neuroidss/FreeEEG32-beta/SetupGuides/images/2.7.PNG

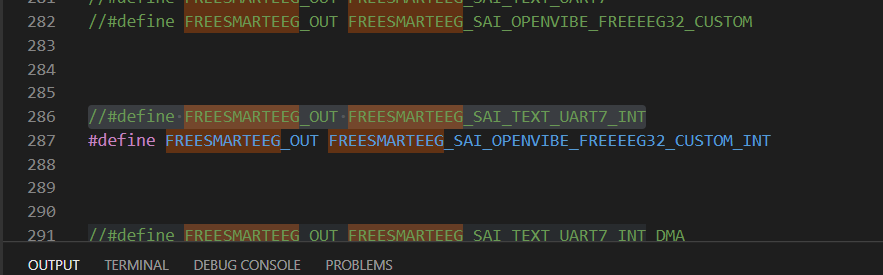
SetupGuides/images/2.7.PNG
