neuroidss/FreeEEG32-beta/SetupGuides/images/test1_2.jpg

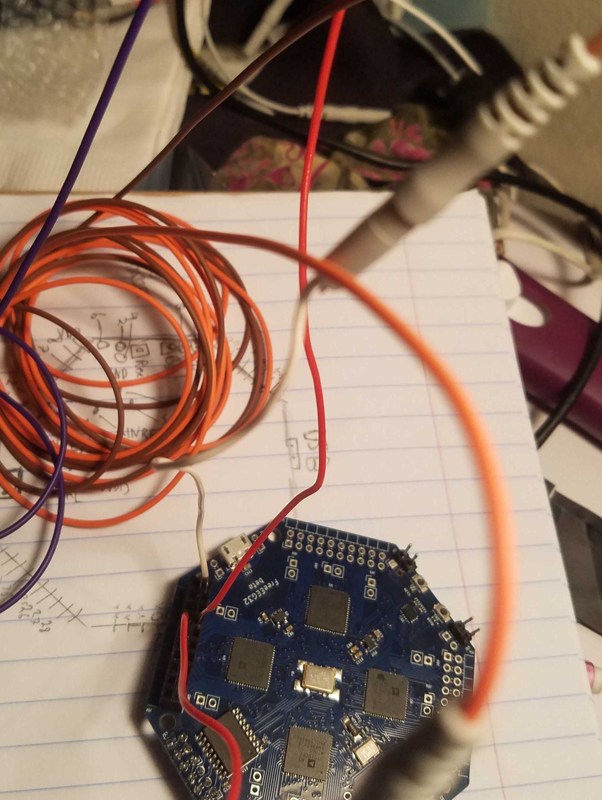
SetupGuides/images/test1_2.jpg
