neuroidss/FreeEEG32-beta/Firmware/AC6/STM32H743ZI_alpha1.5_SD_CDC/Src/ad7779.c

/***************************************************************************//**
 *   @file   ad7779.c
 *   @brief  Implementation of AD7779 Driver.
 *   @author DBogdan (dragos.bogdan@analog.com)
********************************************************************************
 * Copyright 2016(c) Analog Devices, Inc.
 *
 * All rights reserved.
 *
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
 * THIS SOFTWARE IS PROVIDED BY ANALOG DEVICES "AS IS" AND ANY EXPRESS OR
 * IMPLIED WARRANTIES, INCLUDING, BUT NOT LIMITED TO, NON-INFRINGEMENT,
 * MERCHANTABILITY AND FITNESS FOR A PARTICULAR PURPOSE ARE DISCLAIMED.
 * IN NO EVENT SHALL ANALOG DEVICES BE LIABLE FOR ANY DIRECT, INDIRECT,
 * INCIDENTAL, SPECIAL, EXEMPLARY, OR CONSEQUENTIAL DAMAGES (INCLUDING, BUT NOT
 * LIMITED TO, INTELLECTUAL PROPERTY RIGHTS, PROCUREMENT OF SUBSTITUTE GOODS OR
 * SERVICES; LOSS OF USE, DATA, OR PROFITS; OR BUSINESS INTERRUPTION) HOWEVER
 * CAUSED AND ON ANY THEORY OF LIABILITY, WHETHER IN CONTRACT, STRICT LIABILITY,
 * OR TORT (INCLUDING NEGLIGENCE OR OTHERWISE) ARISING IN ANY WAY OUT OF THE USE
 * OF THIS SOFTWARE, EVEN IF ADVISED OF THE POSSIBILITY OF SUCH DAMAGE.
*******************************************************************************/

/******************************************************************************/
/***************************** Include Files **********************************/
/******************************************************************************/
#include <stdint.h>
#include <stdio.h>
#include <stdlib.h>
#include "platform_drivers.h"
#include "ad7779.h"

/******************************************************************************/
/*************************** Constants Definitions ****************************/
/******************************************************************************/
const uint8_t pin_mode_options[16][4] = {
/*	GAIN_1	GAIN_2	GAIN_4	GAIN_8 */
	{0x03,	0xFF,	0x07,	0xFF},	// DEC_RATE_128, HIGH_RES, EXT_REF
	{0x0A,	0xFF,	0xFF,	0xFF},	// DEC_RATE_128, HIGH_RES, INT_REF
	{0x0D,	0xFF,	0xFF,	0xFF},	// DEC_RATE_128, LOW_PWR, EXT_REF
	{0x0E,	0xFF,	0xFF,	0xFF},	// DEC_RATE_128, LOW_PWR, INT_REF
	{0x02,	0x04,	0x06,	0xFF},	// DEC_RATE_256, HIGH_RES, EXT_REF
	{0x09,	0xFF,	0xFF,	0xFF},	// DEC_RATE_256, HIGH_RES, INT_REF
	{0x0C,	0xFF,	0xFF,	0xFF},	// DEC_RATE_256, LOW_PWR, EXT_REF
	{0x0F,	0xFF,	0xFF,	0xFF},	// DEC_RATE_256, LOW_PWR, INT_REF
	{0x01,	0xFF,	0x05,	0xFF},	// DEC_RATE_512, HIGH_RES, EXT_REF
	{0x08,	0xFF,	0xFF,	0xFF},	// DEC_RATE_512, HIGH_RES, INT_REF
	{0x08,	0xFF,	0xFF,	0xFF},	// DEC_RATE_512, LOW_PWR, EXT_REF
	{0xFF,	0xFF,	0xFF,	0xFF},	// DEC_RATE_512, LOW_PWR, INT_REF
	{0x00,	0xFF,	0xFF,	0xFF},	// DEC_RATE_1024, HIGH_RES, EXT_REF
	{0xFF,	0xFF,	0xFF,	0xFF},	// DEC_RATE_1024, HIGH_RES, INT_REF
	{0xFF,	0xFF,	0xFF,	0xFF},	// DEC_RATE_1024, LOW_PWR, EXT_REF
	{0xFF,	0xFF,	0xFF,	0xFF},	// DEC_RATE_1024, LOW_PWR, INT_REF	
};

/******************************************************************************/
/************************** Functions Implementation **************************/
/******************************************************************************/
/**
 * Compute CRC8 checksum.
 * @param data - The data buffer.
 * @param data_size - The size of the data buffer.
 * @return CRC8 checksum.
 */
uint8_t ad7779_compute_crc8(uint8_t *data,
							uint8_t data_size)
{
	uint8_t i;
	uint8_t crc = 0;

	while (data_size) {
		for (i = 0x80; i != 0; i >>= 1) {
			if (((crc & 0x80) != 0) != ((*data & i) != 0)) {
				crc <<= 1;
				crc ^= AD7779_CRC8_POLY;
			} else
				crc <<= 1;
		}
		data++;
		data_size--;
	}

	return crc;
}

/**
 * SPI internal register read from device.
 * @param dev - The device structure.
 * @param reg_addr - The register address.
 * @param reg_data - The register data.
 * @return SUCCESS in case of success, negative error code otherwise.
 */
int32_t ad7779_spi_int_reg_read(ad7779_dev *dev,
								uint8_t reg_addr,
								uint8_t *reg_data)
{
  uint8_t txbuf[3];
  uint8_t rxbuf[3];
	uint8_t buf_size = 2;
	uint8_t crc;
	int32_t ret;

	txbuf[0] = 0x80 | (reg_addr & 0x7F);
	txbuf[1] = 0x00;
	txbuf[2] = 0x00;
	if (dev->spi_crc_en == AD7779_ENABLE)
		buf_size = 3;
	ret = spi_write_and_read(dev->spi_dev.dev, dev->spi_dev.chip_select_port, dev->spi_dev.chip_select_pin, txbuf, rxbuf, buf_size);

	*reg_data = rxbuf[1];
	if (dev->spi_crc_en == AD7779_ENABLE) {
		rxbuf[0] = 0x80 | (reg_addr & 0x7F);
		crc = ad7779_compute_crc8(&rxbuf[0], 2);
		if (crc != rxbuf[2]) {
			printf("%s: CRC Error.\n", __func__);
			ret = FAILURE;
		}
	}

	return ret;
}

/**
 * SPI internal register write to device.
 * @param dev - The device structure.
 * @param reg_addr - The register address.
 * @param reg_data - The register data.
 * @return SUCCESS in case of success, negative error code otherwise.
 */
int32_t ad7779_spi_int_reg_write(ad7779_dev *dev,
								 uint8_t reg_addr,
								 uint8_t reg_data)
{
  uint8_t txbuf[3];
  uint8_t rxbuf[3];
	uint8_t buf_size = 2;
	int32_t ret;

	txbuf[0] = 0x00 | (reg_addr & 0x7F);
	txbuf[1] = reg_data;
	if (dev->spi_crc_en == AD7779_ENABLE) {
		txbuf[2] = ad7779_compute_crc8(&txbuf[0], 2);
		buf_size = 3;
	}
	ret = spi_write_and_read(dev->spi_dev.dev, dev->spi_dev.chip_select_port, dev->spi_dev.chip_select_pin, txbuf, rxbuf, buf_size);
	dev->cached_reg_val[reg_addr] = reg_data;

	return ret;
}

/**
 * SPI internal register read from device using a mask.
 * @param dev - The device structure.
 * @param reg_addr - The register address.
 * @param mask - The mask.
 * @param data - The register data.
 * @return SUCCESS in case of success, negative error code otherwise.
 */
int32_t ad7779_spi_int_reg_read_mask(ad7779_dev *dev,
									 uint8_t reg_addr,
									 uint8_t mask,
									 uint8_t *data)
{
	uint8_t reg_data;
	int32_t ret;

	ret = ad7779_spi_int_reg_read(dev, reg_addr, &reg_data);
	*data = (reg_data & mask);

	return ret;
}

/**
 * SPI internal register write to device using a mask.
 * @param dev - The device structure.
 * @param reg_addr - The register address.
 * @param mask - The mask.
 * @param data - The register data.
 * @return SUCCESS in case of success, negative error code otherwise.
 */
int32_t ad7779_spi_int_reg_write_mask(ad7779_dev *dev,
									  uint8_t reg_addr,
									  uint8_t mask,
									  uint8_t data)
{
	uint8_t reg_data;
	int32_t ret;

	reg_data = dev->cached_reg_val[reg_addr];
	reg_data &= ~mask;
	reg_data |= data;
	ret = ad7779_spi_int_reg_write(dev, reg_addr, reg_data);

	return ret;
}

/**
 * SPI SAR conversion code read.
 * @param dev - The device structure.
 * @param mux_next_conv - The SAR mux input configuration for the next
 *						  conversion.
 * 						  Accepted values: AD7779_AUXAINP_AUXAINN
 *										   AD7779_DVBE_AVSSX
 *										   AD7779_REF1P_REF1N
 *										   AD7779_REF2P_REF2N
 *										   AD7779_REF_OUT_AVSSX
 *										   AD7779_VCM_AVSSX
 *										   AD7779_AREG1CAP_AVSSX_ATT
 *										   AD7779_AREG2CAP_AVSSX_ATT
 *										   AD7779_DREGCAP_DGND_ATT
 *										   AD7779_AVDD1A_AVSSX_ATT
 *										   AD7779_AVDD1B_AVSSX_ATT
 *										   AD7779_AVDD2A_AVSSX_ATT
 *										   AD7779_AVDD2B_AVSSX_ATT
 *										   AD7779_IOVDD_DGND_ATT
 *										   AD7779_AVDD4_AVSSX
 *										   AD7779_DGND_AVSS1A_ATT
 *										   AD7779_DGND_AVSS1B_ATT
 *										   AD7779_DGND_AVSSX_ATT
 *										   AD7779_AVDD4_AVSSX_ATT
 *										   AD7779_REF1P_AVSSX
 *										   AD7779_REF2P_AVSSX
 *										   AD7779_AVSSX_AVDD4_ATT
 * @param sar_code - SAR conversion code.
 * @return SUCCESS in case of success, negative error code otherwise.
 */
int32_t ad7779_spi_sar_read_code(ad7779_dev *dev,
								 ad7779_sar_mux mux_next_conv,
								 uint16_t *sar_code)
{
  uint8_t txbuf[3];
  uint8_t rxbuf[3];
	uint8_t buf_size = 2;
	uint8_t crc;
	int32_t ret;

	txbuf[0] = 0x00 | (AD7779_REG_GLOBAL_MUX_CONFIG & 0x7F);
	txbuf[1] = AD7779_GLOBAL_MUX_CTRL(mux_next_conv);
	if (dev->spi_crc_en == AD7779_ENABLE) {
		txbuf[2] = ad7779_compute_crc8(&txbuf[0], 2);
		buf_size = 3;
	}
	ret = spi_write_and_read(dev->spi_dev.dev, dev->spi_dev.chip_select_port, dev->spi_dev.chip_select_pin, txbuf, rxbuf, buf_size);
	dev->cached_reg_val[AD7779_REG_GLOBAL_MUX_CONFIG] =
									AD7779_GLOBAL_MUX_CTRL(mux_next_conv);
	rxbuf[0] = rxbuf[0] & 0x0F;
	*sar_code = (rxbuf[0] << 8) | rxbuf[1];
	if (dev->spi_crc_en == AD7779_ENABLE) {
		crc = ad7779_compute_crc8(&rxbuf[0], 2);
		if (crc != rxbuf[2]) {
			printf("%s: CRC Error.\n", __func__);
			ret = FAILURE;
		}
	}

	return ret;
}

/**
 * Set SPI operation mode.
 * @param dev - The device structure.
 * @param mode - The SPI operation mode.
 *				 Accepted values: AD7779_INT_REG
 *								  AD7779_SD_CONV
 *								  AD7779_SAR_CONV
 * @return SUCCESS in case of success, negative error code otherwise.
 */
int32_t ad7779_set_spi_op_mode(ad7779_dev *dev,
							   ad7779_spi_op_mode mode)
{
	int32_t ret;
	uint8_t cfg_2;
	uint8_t cfg_3;

	switch (mode) {
	case AD7779_SD_CONV:
		cfg_2 = 0;
		cfg_3 = AD7779_SPI_SLAVE_MODE_EN;
		break;
	case AD7779_SAR_CONV:
		cfg_2 = AD7779_SAR_DIAG_MODE_EN;
		cfg_3 = 0;
		break;
	default:	// AD7779_INT_REG
		cfg_2 = 0;
		cfg_3 = 0;
	}
	ret = ad7779_spi_int_reg_write_mask(dev,
										AD7779_REG_GENERAL_USER_CONFIG_2,
										AD7779_SAR_DIAG_MODE_EN,
										cfg_2);
	ret |= ad7779_spi_int_reg_write_mask(dev,
										 AD7779_REG_GENERAL_USER_CONFIG_3,
										 AD7779_SPI_SLAVE_MODE_EN,
										 cfg_3);
	dev->spi_op_mode = mode;

	return ret;
}

/**
 * Get SPI operation mode.
 * @param dev - The device structure.
 * @param mode - The SPI operation mode.
 * @return SUCCESS in case of success, negative error code otherwise.
 */
int32_t ad7779_get_spi_op_mode(ad7779_dev *dev,
							   ad7779_spi_op_mode *mode)
{
	*mode = dev->spi_op_mode;

	return SUCCESS;
}

/**
 * Update the state of the MODEx pins according to the settings specified in
 * the device structure.
 * @param dev - The device structure.
 * @return SUCCESS in case of success, negative error code otherwise.
 */
int32_t ad7779_do_update_mode_pins(ad7779_dev *dev)
{
	int32_t ret;
	uint8_t option_index;
	uint8_t mode;

	if (!(dev->gain[AD7779_CH0] == dev->gain[AD7779_CH1] ==
		  dev->gain[AD7779_CH2] == dev->gain[AD7779_CH3] == AD7779_GAIN_1))
		goto error;

	if (!(dev->gain[AD7779_CH4] == dev->gain[AD7779_CH5] ==
		  dev->gain[AD7779_CH6] == dev->gain[AD7779_CH6]))
		goto error;

	switch (dev->dec_rate_int) {
	case 128:
		option_index = 0;
		break;
	case 256:
		option_index = 4;
		break;
	case 512:
		option_index = 8;
		break;
	case 1024:
		option_index = 12;
		break;
	default:
		goto error;
	}

	if (dev->pwr_mode == AD7779_HIGH_RES)
		if (dev->ref_type == AD7779_EXT_REF)
			mode = pin_mode_options[option_index + 0][dev->gain[AD7779_CH4]];
		else
			mode = pin_mode_options[option_index + 1][dev->gain[AD7779_CH4]];
	else
		if (dev->ref_type == AD7779_EXT_REF)
			mode = pin_mode_options[option_index + 2][dev->gain[AD7779_CH4]];
		else
			mode = pin_mode_options[option_index + 3][dev->gain[AD7779_CH4]];

	if (mode == 0xFF)
	  goto error;

	ret = gpio_set_value(&dev->gpio_dev,
					dev->gpio_mode0,
					((mode & 0x01) >> 0));
	ret |= gpio_set_value(&dev->gpio_dev,
					dev->gpio_mode1,
					((mode & 0x02) >> 1));
	ret |= gpio_set_value(&dev->gpio_dev,
					dev->gpio_mode2,
					((mode & 0x04) >> 2));
	ret |= gpio_set_value(&dev->gpio_dev,
					dev->gpio_mode3,
					((mode & 0x08) >> 3));

	/* All the pins that define the AD7779 configuration mode are re-evaluated
	 * every time SYNC_IN pin is pulsed. */
	ret |= gpio_set_value(&dev->gpio_dev, dev->gpio_sync_in, GPIO_LOW);
	mdelay(10);
	ret |= gpio_set_value(&dev->gpio_dev, dev->gpio_sync_in, GPIO_HIGH);

	return ret;

error:
	printf("%s: This setting can't be set in PIN control mode.\n",
		   __func__);
	return FAILURE;
}

/**
 * Set the state (enable, disable) of the channel.
 * @param dev - The device structure.
 * @param ch - The channel number.
 * 			   Accepted values: AD7779_CH0
 * 			   					AD7779_CH1
 * 			   					AD7779_CH2
 * 			   					AD7779_CH3
 * 			   					AD7779_CH4
 * 			   					AD7779_CH5
 * 			   					AD7779_CH6
 * 			   					AD7779_CH7
 * @param state - The channel state.
 * 				  Accepted values: AD7779_ENABLE
 * 								   AD7779_DISABLE
 * @return SUCCESS in case of success, negative error code otherwise.
 */
int32_t ad7779_set_state(ad7779_dev *dev,
						 ad7779_ch ch,
						 ad7779_state state)
{
	int32_t ret;

	ret = ad7779_spi_int_reg_write_mask(dev,
										AD7779_REG_CH_DISABLE,
										AD7779_CH_DISABLE(0x1),
										AD7779_CH_DISABLE(state));
	dev->state[ch] = state;

	return ret;
}

/**
 * Get the state (enable, disable) of the selected channel.
 * @param dev - The device structure.
 * @param ch - The channel number.
 * 			   Accepted values: AD7779_CH0
 * 			   					AD7779_CH1
 * 			   					AD7779_CH2
 * 			   					AD7779_CH3
 * 			   					AD7779_CH4
 * 			   					AD7779_CH5
 * 			   					AD7779_CH6
 * 			   					AD7779_CH7
 * @param state - The channel state.
 * @return SUCCESS in case of success, negative error code otherwise.
 */
int32_t ad7779_get_state(ad7779_dev *dev,
						 ad7779_ch ch,
						 ad7779_state *state)
{
	*state = dev->state[ch];

	return SUCCESS;
}

/**
 * Set the gain of the selected channel.
 * @param dev - The device structure.
 * @param ch - The channel number.
 * 			   Accepted values: AD7779_CH0
 * 			   					AD7779_CH1
 * 			   					AD7779_CH2
 * 			   					AD7779_CH3
 * 			   					AD7779_CH4
 * 			   					AD7779_CH5
 * 			   					AD7779_CH6
 * 			   					AD7779_CH7
 * @param gain - The gain value.
 * 				 Accepted values: AD7779_GAIN_1
 * 								  AD7779_GAIN_2
 * 								  AD7779_GAIN_4
 * 								  AD7779_GAIN_8
 * @return SUCCESS in case of success, negative error code otherwise.
 */
int32_t ad7779_set_gain(ad7779_dev *dev,
						ad7779_ch ch,
						ad7779_gain gain)
{
	int32_t ret;

	if (dev->ctrl_mode == AD7779_PIN_CTRL) {
		if (ch <= AD7779_CH3) {
			dev->gain[AD7779_CH0] = gain;
			dev->gain[AD7779_CH1] = gain;
			dev->gain[AD7779_CH2] = gain;
			dev->gain[AD7779_CH3] = gain;
		} else {
			dev->gain[AD7779_CH4] = gain;
			dev->gain[AD7779_CH5] = gain;
			dev->gain[AD7779_CH6] = gain;
			dev->gain[AD7779_CH7] = gain;
		}
		ret = ad7779_do_update_mode_pins(dev);
	} else {
		dev->gain[ch] = gain;
		ret = ad7779_spi_int_reg_write_mask(dev,
											AD7779_REG_CH_CONFIG(ch),
											AD7779_CH_GAIN(0x3),
											AD7779_CH_GAIN(gain));
	}

	return ret;
}

/**
 * Get the gain of the selected channel.
 * @param dev - The device structure.
 * @param ch - The channel number.
 * 			   Accepted values: AD7779_CH0
 * 			   					AD7779_CH1
 * 			   					AD7779_CH2
 * 			   					AD7779_CH3
 * 			   					AD7779_CH4
 * 			   					AD7779_CH5
 * 			   					AD7779_CH6
 * 			   					AD7779_CH7
 * @param gain - The gain value.
 * @return SUCCESS in case of success, negative error code otherwise.
 */
int32_t ad7779_get_gain(ad7779_dev *dev,
						ad7779_ch ch,
						ad7779_gain *gain)
{
	*gain = dev->gain[ch];

	return SUCCESS;
}

/**
 * Set the decimation rate.
 * @param dev - The device structure.
 * @param integer_val - The integer value.
 * @param decimal_val - The decimal value.
 * @return SUCCESS in case of success, negative error code otherwise.
 */
int32_t ad7779_set_dec_rate(ad7779_dev *dev,
							uint16_t int_val,
							uint16_t dec_val)
{
	int32_t ret;
	uint8_t msb;
	uint8_t lsb;

	if (dev->ctrl_mode == AD7779_PIN_CTRL) {
		switch (int_val) {
		case 128:
			break;
		case 256:
			break;
		case 512:
			break;
		case 1024:
			break;
		default:
			printf("%s: This setting can't be set in PIN control mode.\n",
				   __func__);
			return FAILURE;
		}
		dev->dec_rate_int = int_val;
		dev->dec_rate_int = dec_val;
		ret = ad7779_do_update_mode_pins(dev);
	} else {
		msb = (int_val & 0x0F00) >> 8;
		lsb = (int_val & 0x00FF) >> 0;
		ret = ad7779_spi_int_reg_write(dev,
									   AD7779_REG_SRC_N_MSB,
									   msb);
		ret |= ad7779_spi_int_reg_write(dev,
										AD7779_REG_SRC_N_LSB,
										lsb);
		dec_val = (dec_val * 65536) / 1000;
		msb = (dec_val & 0xFF00) >> 8;
		lsb = (dec_val & 0x00FF) >> 0;
		ret |= ad7779_spi_int_reg_write(dev,
										AD7779_REG_SRC_IF_MSB,
										msb);
		ret |= ad7779_spi_int_reg_write(dev,
										AD7779_REG_SRC_IF_LSB,
										lsb);
		dev->dec_rate_int = int_val;
		dev->dec_rate_int = dec_val;
	}

	return ret;
}

/**
 * Get the decimation rate.
 * @param dev - The device structure.
 * @param integer_val - The integer value.
 * @param decimal_val - The decimal value.
 * @return SUCCESS in case of success, negative error code otherwise.
 */
int32_t ad7779_get_dec_rate(ad7779_dev *dev,
							uint16_t *int_val,
							uint16_t *dec_val)
{
	*int_val = dev->dec_rate_int;
	*dec_val = dev->dec_rate_int;

	return SUCCESS;
}

/**
 * Set the power mode.
 * @param dev - The device structure.
 * @param pwr_mode - The power mode.
 * 					 Accepted values: AD7779_HIGH_RES
 *									  AD7779_LOW_PWR
 * @return SUCCESS in case of success, negative error code otherwise.
 */
int32_t ad7779_set_power_mode(ad7779_dev *dev,
							  ad7779_pwr_mode pwr_mode)
{
	int32_t ret;

	ret = ad7779_spi_int_reg_write_mask(dev,
										AD7779_REG_GENERAL_USER_CONFIG_1,
										AD7779_MOD_POWERMODE,
										pwr_mode ? AD7779_MOD_POWERMODE : 0);
	dev->pwr_mode = pwr_mode;

	return ret;
}

/**
 * Get the power mode.
 * @param dev - The device structure.
 * @param pwr_mode - The power mode.
 * @return SUCCESS in case of success, negative error code otherwise.
 */
int32_t ad7779_get_power_mode(ad7779_dev *dev,
							  ad7779_pwr_mode *pwr_mode)
{
	*pwr_mode = dev->pwr_mode;

	return SUCCESS;
}

/**
 * Set the reference type.
 * @param dev - The device structure.
 * @param pwr_mode - The reference type.
 * 					 Accepted values: AD7779_EXT_REF
 *									  AD7779_INT_REF
 * @return SUCCESS in case of success, negative error code otherwise.
 */
int32_t ad7779_set_reference_type(ad7779_dev *dev,
								  ad7779_ref_type ref_type)
{
	int32_t ret;

	ret = ad7779_spi_int_reg_write_mask(dev,
										AD7779_REG_GENERAL_USER_CONFIG_1,
										AD7779_PDB_REFOUT_BUF,
										ref_type ? AD7779_PDB_REFOUT_BUF : 0);
	dev->ref_type = ref_type;

	return ret;
}

/**
 * Get the reference type.
 * @param dev - The device structure.
 * @param pwr_mode - The reference type.
 * @return SUCCESS in case of success, negative error code otherwise.
 */
int32_t ad7779_get_reference_type(ad7779_dev *dev,
								  ad7779_ref_type *ref_type)
{
	*ref_type = dev->ref_type;

	return SUCCESS;
}

/**
 * Set the DCLK divider.
 * @param dev - The device structure.
 * @param div - The DCLK divider.
 *				Accepted values: AD7779_DCLK_DIV_1
 *								 AD7779_DCLK_DIV_2
 *								 AD7779_DCLK_DIV_4
 *								 AD7779_DCLK_DIV_8
 *								 AD7779_DCLK_DIV_16
 *								 AD7779_DCLK_DIV_32
 *								 AD7779_DCLK_DIV_64
 *								 AD7779_DCLK_DIV_128
 * @return SUCCESS in case of success, negative error code otherwise.
 */
int32_t ad7779_set_dclk_div(ad7779_dev *dev,
							ad7768_dclk_div div)
{
	int32_t ret;

	if (dev->ctrl_mode == AD7779_PIN_CTRL) {
		ret = gpio_set_value(&dev->gpio_dev,
						dev->gpio_dclk0,
						((div & 0x01) >> 0));
		ret |= gpio_set_value(&dev->gpio_dev,
						dev->gpio_dclk1,
						((div & 0x02) >> 1));
		ret |= gpio_set_value(&dev->gpio_dev,
						dev->gpio_dclk2,
						((div & 0x04) >> 2));
	} else {
		ret = ad7779_spi_int_reg_write_mask(dev,
											AD7779_REG_CH_DISABLE,
											AD7779_DCLK_CLK_DIV(0x3),
											AD7779_DCLK_CLK_DIV(div));
	}
	dev->dclk_div = div;

	return ret;
}

/**
 * Get the DCLK divider.
 * @param dev - The device structure.
 * @param div - The DCLK divider.
 * @return SUCCESS in case of success, negative error code otherwise.
 */
int32_t ad7779_get_dclk_div(ad7779_dev *dev,
							ad7768_dclk_div *div)
{
	*div = dev->dclk_div;

	return SUCCESS;
}

/**
 * Set the synchronization offset of the selected channel.
 * @param dev - The device structure.
 * @param ch - The channel number.
 * 			   Accepted values: AD7779_CH0
 * 			   					AD7779_CH1
 * 			   					AD7779_CH2
 * 			   					AD7779_CH3
 * 			   					AD7779_CH4
 * 			   					AD7779_CH5
 * 			   					AD7779_CH6
 * 			   					AD7779_CH7
 * @param sync_offset - The synchronization offset value.
 * @return SUCCESS in case of success, negative error code otherwise.
 */
int32_t ad7779_set_sync_offset(ad7779_dev *dev,
							   ad7779_ch ch,
							   uint8_t sync_offset)
{
	int32_t ret;

	if (dev->ctrl_mode == AD7779_PIN_CTRL) {
		printf("%s: This feature is not available in PIN control mode.\n",
			   __func__);
		return FAILURE;
	}

	ret = ad7779_spi_int_reg_write(dev,
								   AD7779_REG_CH_SYNC_OFFSET(ch),
								   sync_offset);
	dev->sync_offset[ch] = sync_offset;

	return ret;
}

/**
 * Get the synchronization offset of the selected channel.
 * @param dev - The device structure.
 * @param ch - The channel number.
 * 			   Accepted values: AD7779_CH0
 * 			   					AD7779_CH1
 * 			   					AD7779_CH2
 * 			   					AD7779_CH3
 * 			   					AD7779_CH4
 * 			   					AD7779_CH5
 * 			   					AD7779_CH6
 * 			   					AD7779_CH7
 * @param sync_offset - The synchronization offset value.
 * @return SUCCESS in case of success, negative error code otherwise.
 */
int32_t ad7779_get_sync_offset(ad7779_dev *dev,
							   ad7779_ch ch,
							   uint8_t *sync_offset)
{
	if (dev->ctrl_mode == AD7779_PIN_CTRL) {
		printf("%s: This feature is not available in PIN control mode.\n",
			   __func__);
		return FAILURE;
	}

	*sync_offset = dev->sync_offset[ch];

	return SUCCESS;
}

/**
 * Set the offset correction of the selected channel.
 * @param dev - The device structure.
 * @param ch - The channel number.
 * 			   Accepted values: AD7779_CH0
 * 			   					AD7779_CH1
 * 			   					AD7779_CH2
 * 			   					AD7779_CH3
 * 			   					AD7779_CH4
 * 			   					AD7779_CH5
 * 			   					AD7779_CH6
 * 			   					AD7779_CH7
 * @param offset - The offset value.
 * @return SUCCESS in case of success, negative error code otherwise.
 */
int32_t ad7779_set_offset_corr(ad7779_dev *dev,
							   ad7779_ch ch,
							   uint32_t offset)
{
	int32_t ret;
	uint8_t upper_uint8_t;
	uint8_t mid_uint8_t;
	uint8_t lower_uint8_t;

	if (dev->ctrl_mode == AD7779_PIN_CTRL) {
		printf("%s: This feature is not available in PIN control mode.\n",
			   __func__);
		return FAILURE;
	}

	upper_uint8_t = (offset & 0xFF0000) >> 16;
	mid_uint8_t = (offset & 0x00FF00) >> 8;
	lower_uint8_t = (offset & 0x0000FF) >> 0;
	ret = ad7779_spi_int_reg_write(dev,
								   AD7779_REG_CH_OFFSET_UPPER_BYTE(ch),
								   upper_uint8_t);
	ret |= ad7779_spi_int_reg_write(dev,
									AD7779_REG_CH_OFFSET_MID_BYTE(ch),
									mid_uint8_t);
	ret |= ad7779_spi_int_reg_write(dev,
									AD7779_REG_CH_OFFSET_LOWER_BYTE(ch),
									lower_uint8_t);
	dev->offset_corr[ch] = offset;

	return ret;
}

/**
 * Get the offset correction of the selected channel.
 * @param dev - The device structure.
 * @param ch - The channel number.
 * 			   Accepted values: AD7779_CH0
 * 			   					AD7779_CH1
 * 			   					AD7779_CH2
 * 			   					AD7779_CH3
 * 			   					AD7779_CH4
 * 			   					AD7779_CH5
 * 			   					AD7779_CH6
 * 			   					AD7779_CH7
 * @param offset - The offset value.
 * @return SUCCESS in case of success, negative error code otherwise.
 */
int32_t ad7779_get_offset_corr(ad7779_dev *dev,
							   ad7779_ch ch,
							   uint32_t *offset)
{
	if (dev->ctrl_mode == AD7779_PIN_CTRL) {
		printf("%s: This feature is not available in PIN control mode.\n",
			   __func__);
		return FAILURE;
	}

	*offset = dev->offset_corr[ch];

	return SUCCESS;
}

/**
 * Set the gain correction of the selected channel.
 * @param dev - The device structure.
 * @param ch - The channel number.
 * 			   Accepted values: AD7779_CH0
 * 			   					AD7779_CH1
 * 			   					AD7779_CH2
 * 			   					AD7779_CH3
 * 			   					AD7779_CH4
 * 			   					AD7779_CH5
 * 			   					AD7779_CH6
 * 			   					AD7779_CH7
 * @param gain - The gain value.
 * @return SUCCESS in case of success, negative error code otherwise.
 */
int32_t ad7779_set_gain_corr(ad7779_dev *dev,
							 ad7779_ch ch,
							 uint32_t gain)
{
	int32_t ret;
	uint8_t upper_uint8_t;
	uint8_t mid_uint8_t;
	uint8_t lower_uint8_t;

	if (dev->ctrl_mode == AD7779_PIN_CTRL) {
		printf("%s: This feature is not available in PIN control mode.\n",
			   __func__);
		return FAILURE;
	}

	gain &= 0xFFFFFF;
	upper_uint8_t = (gain & 0xff0000) >> 16;
	mid_uint8_t = (gain & 0x00ff00) >> 8;
	lower_uint8_t = (gain & 0x0000ff) >> 0;
	ret = ad7779_spi_int_reg_write(dev,
								   AD7779_REG_CH_GAIN_UPPER_BYTE(ch),
								   upper_uint8_t);
	ret |= ad7779_spi_int_reg_write(dev,
									AD7779_REG_CH_GAIN_MID_BYTE(ch),
									mid_uint8_t);
	ret |= ad7779_spi_int_reg_write(dev,
									AD7779_REG_CH_GAIN_LOWER_BYTE(ch),
									lower_uint8_t);
	dev->gain_corr[ch] = gain;

	return ret;
}

/**
 * Get the gain correction of the selected channel.
 * @param dev - The device structure.
 * @param ch - The channel number.
 * 			   Accepted values: AD7779_CH0
 * 			   					AD7779_CH1
 * 			   					AD7779_CH2
 * 			   					AD7779_CH3
 * 			   					AD7779_CH4
 * 			   					AD7779_CH5
 * 			   					AD7779_CH6
 * 			   					AD7779_CH7
 * @param gain - The gain value.
 * @return SUCCESS in case of success, negative error code otherwise.
 */
int32_t ad7779_get_gain_corr(ad7779_dev *dev,
							 ad7779_ch ch,
							 uint32_t *gain)
{
	if (dev->ctrl_mode == AD7779_PIN_CTRL) {
		printf("%s: This feature is not available in PIN control mode.\n",
			   __func__);
		return FAILURE;
	}

	*gain = dev->gain_corr[ch];

	return SUCCESS;
}

/**
 * Set the reference buffer operation mode of the selected pin.
 * @param dev - The device structure.
 * @param refx_pin - The selected pin.
 * 					 Accepted values: AD7779_REFX_P
 * 									  AD7779_REFX_N
 * @param mode - The reference buffer operation mode.
 * 				 Accepted values: AD7779_REF_BUF_ENABLED
 * 								  AD7779_REF_BUF_PRECHARGED
 * 								  AD7779_REF_BUF_DISABLED
 * @return SUCCESS in case of success, negative error code otherwise.
 */
int32_t ad7779_set_ref_buf_op_mode(ad7779_dev *dev,
								   ad7779_refx_pin refx_pin,
								   ad7779_ref_buf_op_mode mode)
{
	int32_t ret;
	uint8_t config_1;
	uint8_t config_2;

	if (dev->ctrl_mode == AD7779_PIN_CTRL) {
		printf("%s: This feature is not available in PIN control mode.\n",
			   __func__);
		return FAILURE;
	}

	if (refx_pin == AD7779_REFX_P) {
		switch (mode) {
		case AD7779_REF_BUF_ENABLED:
			config_1 = AD7779_REF_BUF_POS_EN;
			config_2 = 0;
			break;
		case AD7779_REF_BUF_PRECHARGED:
			config_1 = AD7779_REF_BUF_POS_EN;
			config_2 = AD7779_REFBUFP_PREQ;
			break;
		default:
			config_1 = 0;
			config_2 = 0;
		}
		ret = ad7779_spi_int_reg_write_mask(dev,
											AD7779_REG_BUFFER_CONFIG_1,
											AD7779_REF_BUF_POS_EN,
											config_1);
		ret |= ad7779_spi_int_reg_write_mask(dev,
											 AD7779_REG_BUFFER_CONFIG_2,
											 AD7779_REFBUFP_PREQ,
											 config_2);
	} else {
		switch (mode) {
		case AD7779_REF_BUF_ENABLED:
			config_1 = AD7779_REF_BUF_NEG_EN;
			config_2 = 0;
			break;
		case AD7779_REF_BUF_PRECHARGED:
			config_1 = AD7779_REF_BUF_NEG_EN;
			config_2 = AD7779_REFBUFN_PREQ;
			break;
		default:
			config_1 = 0;
			config_2 = 0;
		}
		ret = ad7779_spi_int_reg_write_mask(dev,
											AD7779_REG_BUFFER_CONFIG_1,
											AD7779_REF_BUF_NEG_EN,
											config_1);
		ret |= ad7779_spi_int_reg_write_mask(dev,
											 AD7779_REG_BUFFER_CONFIG_2,
											 AD7779_REFBUFN_PREQ,
											 config_2);
	}
	dev->ref_buf_op_mode[refx_pin] = mode;

	return ret;
}

/**
 * Get the reference buffer operation mode of the selected pin.
 * @param dev - The device structure.
 * @param refx_pin - The selected pin.
 * 					 Accepted values: AD7779_REFX_P
 * 									  AD7779_REFX_N
 * @param mode - The reference buffer operation mode.
 * 				 Accepted values: AD7779_REF_BUF_ENABLED
 * 								  AD7779_REF_BUF_PRECHARGED
 * 								  AD7779_REF_BUF_DISABLED
 * @return SUCCESS in case of success, negative error code otherwise.
 */
int32_t ad7779_get_ref_buf_op_mode(ad7779_dev *dev,
								   ad7779_refx_pin refx_pin,
								   ad7779_ref_buf_op_mode *mode)
{
	if (dev->ctrl_mode == AD7779_PIN_CTRL) {
		printf("%s: This feature is not available in PIN control mode.\n",
			   __func__);
		return FAILURE;
	}

	*mode = dev->ref_buf_op_mode[refx_pin];

	return SUCCESS;
}

/**
 * Set the SAR ADC configuration.
 * @param dev - The device structure.
 * @param state - The SAR ADC state.
 * 				  Accepted values: AD7779_ENABLE
 * 								   AD7779_DISABLE
 * @param mux - The SAR mux input configuration.
 * 				Accepted values: AD7779_AUXAINP_AUXAINN
 *								 AD7779_DVBE_AVSSX
 *								 AD7779_REF1P_REF1N
 *								 AD7779_REF2P_REF2N
 *								 AD7779_REF_OUT_AVSSX
 *								 AD7779_VCM_AVSSX
 *								 AD7779_AREG1CAP_AVSSX_ATT
 *								 AD7779_AREG2CAP_AVSSX_ATT
 *								 AD7779_DREGCAP_DGND_ATT
 *								 AD7779_AVDD1A_AVSSX_ATT
 *								 AD7779_AVDD1B_AVSSX_ATT
 *								 AD7779_AVDD2A_AVSSX_ATT
 *								 AD7779_AVDD2B_AVSSX_ATT
 *								 AD7779_IOVDD_DGND_ATT
 *								 AD7779_AVDD4_AVSSX
 *								 AD7779_DGND_AVSS1A_ATT
 *								 AD7779_DGND_AVSS1B_ATT
 *								 AD7779_DGND_AVSSX_ATT
 *								 AD7779_AVDD4_AVSSX_ATT
 *								 AD7779_REF1P_AVSSX
 *								 AD7779_REF2P_AVSSX
 *								 AD7779_AVSSX_AVDD4_ATT
 * @return SUCCESS in case of success, negative error code otherwise.
 */
int32_t ad7779_set_sar_cfg(ad7779_dev *dev,
						   ad7779_state state,
						   ad7779_sar_mux mux)
{
	int32_t ret;

	ret = ad7779_spi_int_reg_write_mask(dev,
										AD7779_REG_GENERAL_USER_CONFIG_1,
										AD7779_PDB_SAR,
										(state == AD7779_ENABLE) ?
												AD7779_PDB_SAR : 0);
	ret |= ad7779_spi_int_reg_write(dev,
									AD7779_REG_GLOBAL_MUX_CONFIG,
									AD7779_GLOBAL_MUX_CTRL(mux));
	dev->sar_state = state;
	dev->sar_mux = mux;

	return ret;
}

/**
 * Get the SAR ADC configuration.
 * @param dev - The device structure.
 * @param state - The SAR ADC state.
 * @param mux - The SAR mux input configuration.
 * @return SUCCESS in case of success, negative error code otherwise.
 */
int32_t ad7779_get_sar_cfg(ad7779_dev *dev,
						   ad7779_state *state,
						   ad7779_sar_mux *mux)
{
	*state = dev->sar_state;
	*mux = dev->sar_mux;

	return SUCCESS;
}

/**
 * Do a single SAR conversion.
 * @param dev - The device structure.
 * @param mux - The SAR mux input configuration.
 * 				Accepted values: AD7779_AUXAINP_AUXAINN
 *								 AD7779_DVBE_AVSSX
 *								 AD7779_REF1P_REF1N
 *								 AD7779_REF2P_REF2N
 *								 AD7779_REF_OUT_AVSSX
 *								 AD7779_VCM_AVSSX
 *								 AD7779_AREG1CAP_AVSSX_ATT
 *								 AD7779_AREG2CAP_AVSSX_ATT
 *								 AD7779_DREGCAP_DGND_ATT
 *								 AD7779_AVDD1A_AVSSX_ATT
 *								 AD7779_AVDD1B_AVSSX_ATT
 *								 AD7779_AVDD2A_AVSSX_ATT
 *								 AD7779_AVDD2B_AVSSX_ATT
 *								 AD7779_IOVDD_DGND_ATT
 *								 AD7779_AVDD4_AVSSX
 *								 AD7779_DGND_AVSS1A_ATT
 *								 AD7779_DGND_AVSS1B_ATT
 *								 AD7779_DGND_AVSSX_ATT
 *								 AD7779_AVDD4_AVSSX_ATT
 *								 AD7779_REF1P_AVSSX
 *								 AD7779_REF2P_AVSSX
 *								 AD7779_AVSSX_AVDD4_ATT
 * @param sar_code - SAR conversion code.
 * @return SUCCESS in case of success, negative error code otherwise.
 */
int32_t ad7779_do_single_sar_conv(ad7779_dev *dev,
								  ad7779_sar_mux mux,
								  uint16_t *sar_code)
{
	ad7779_spi_op_mode restore_spi_op_mode;
	ad7779_state restore_sar_state;
	int32_t ret;

	restore_spi_op_mode = dev->spi_op_mode;
	restore_sar_state = dev->sar_state;
	ret = ad7779_set_sar_cfg(dev, AD7779_ENABLE, mux);
	ret |= ad7779_set_spi_op_mode(dev, AD7779_SAR_CONV);
	ret |= gpio_set_value(&dev->gpio_dev, dev->gpio_convst_sar, GPIO_LOW);
	mdelay(10);	// Acquisition Time = min 500 ns
	ret |= gpio_set_value(&dev->gpio_dev, dev->gpio_convst_sar, GPIO_HIGH);
	mdelay(10);	// Conversion Time = max 3.4 us
	ad7779_spi_sar_read_code(dev, mux, sar_code);
	ret |= ad7779_set_sar_cfg(dev, restore_sar_state, mux);
	ret |= ad7779_set_spi_op_mode(dev, restore_spi_op_mode);

	return ret;
}

/**
 * Do a SPI software reset.
 * @param dev - The device structure.
 * @return SUCCESS in case of success, negative error code otherwise.
 */
int32_t ad7779_do_spi_soft_reset(ad7779_dev *dev)
{
  uint8_t txbuf[8] = {0xFF, 0xFF, 0xFF, 0xFF, 0xFF, 0xFF, 0xFF, 0xFF};
  uint8_t rxbuf[8] = {0xFF, 0xFF, 0xFF, 0xFF, 0xFF, 0xFF, 0xFF, 0xFF};
	int32_t ret;

	/* Keeping the SDI pin high during 64 consecutives clocks generates a
	   software reset */
	ret = spi_write_and_read(dev->spi_dev.dev, dev->spi_dev.chip_select_port, dev->spi_dev.chip_select_pin, txbuf, rxbuf, 8);

	return ret;
}

/**
 * Set the state (enable, disable) of the SINC5 filter.
 * @param dev - The device structure.
 * @param state - The SINC5 filter state.
 * 				  Accepted values: AD7779_ENABLE
 * 								   AD7779_DISABLE
 * @return SUCCESS in case of success, negative error code otherwise.
 */
int32_t ad7771_set_sinc5_filter_state(ad7779_dev *dev,
									  ad7779_state state)
{
	int32_t ret;

	if (dev->ctrl_mode == AD7779_PIN_CTRL) {
		printf("%s: This feature is not available in PIN control mode.\n",
			   __func__);
		return FAILURE;
	}

	ret = ad7779_spi_int_reg_write_mask(dev,
										AD7779_REG_GENERAL_USER_CONFIG_2,
										AD7771_FILTER_MODE,
										(state == AD7779_ENABLE) ?
												AD7771_FILTER_MODE : 0);
	dev->sinc5_state = state;

	return ret;
}

/**
 * Get the state (enable, disable) of the SINC5 filter.
 * @param dev - The device structure.
 * @param state - The SINC5 filter state.
 * @return SUCCESS in case of success, negative error code otherwise.
 */
int32_t ad7771_get_sinc5_filter_state(ad7779_dev *dev,
									  ad7779_state *state)
{
	if (dev->ctrl_mode == AD7779_PIN_CTRL) {
		printf("%s: This feature is not available in PIN control mode.\n",
			   __func__);
		return FAILURE;
	}

	*state = dev->sinc5_state;

	return SUCCESS;
}

/**
 * Initialize the device.
 * @param device - The device structure.
 * @param init_param - The structure that contains the device initial
 * 					   parameters.
 * @return SUCCESS in case of success, negative error code otherwise.
 */
int32_t ad7779_setup(ad7779_dev **device,
					 ad7779_init_param init_param)
{
	ad7779_dev *dev;
	uint8_t i;
	int32_t ret;

  if (!dev)
  {
    dev = (ad7779_dev *)malloc(sizeof(*dev));
  }
//	dev = (ad7779_dev *)malloc(sizeof(*dev));
	if (!dev) {
		return -1;
	}

	/* SPI */
//	dev->spi_dev.chip_select = init_param.spi_chip_select;
//  dev->spi_dev.chip_select_port = init_param.spi_chip_select_port;
//  dev->spi_dev.chip_select_pin = init_param.spi_chip_select_pin;
//	dev->spi_dev.mode = init_param.spi_mode;
//	dev->spi_dev.device_id = init_param.spi_device_id;
	//  dev->spi_dev.type = init_param.spi_type;
	dev->spi_dev = init_param.spi_dev;
	ret = spi_init(dev->spi_dev.dev);
//	dev->gpio_dev.device_id = init_param.gpio_device_id;
//	dev->gpio_dev.type = init_param.gpio_type;
	ret |= gpio_init(&dev->gpio_dev);

/*
	// GPIO
	dev->gpio_reset = init_param.gpio_reset;
	dev->gpio_mode0 = init_param.gpio_mode0;
	dev->gpio_mode1 = init_param.gpio_mode1;
	dev->gpio_mode2 = init_param.gpio_mode2;
	dev->gpio_mode3 = init_param.gpio_mode3;
	dev->gpio_dclk0 = init_param.gpio_dclk0;
	dev->gpio_dclk1 = init_param.gpio_dclk1;
	dev->gpio_dclk2 = init_param.gpio_dclk2;
	dev->gpio_sync_in = init_param.gpio_sync_in;
	dev->gpio_convst_sar = init_param.gpio_convst_sar;

	ret |= gpio_set_direction(&dev->gpio_dev, dev->gpio_reset, GPIO_OUT);
	ret |= gpio_set_value(&dev->gpio_dev, dev->gpio_reset, GPIO_LOW);
	mdelay(10);	// RESET Hold Time = min 2 � MCLK
	ret |= gpio_set_value(&dev->gpio_dev, dev->gpio_reset, GPIO_HIGH);
	mdelay(10);	// RESET Rising Edge to First DRDY = min 225 us
	ret |= gpio_set_direction(&dev->gpio_dev, dev->gpio_mode0, GPIO_OUT);
	ret |= gpio_set_direction(&dev->gpio_dev, dev->gpio_mode1, GPIO_OUT);
	ret |= gpio_set_direction(&dev->gpio_dev, dev->gpio_mode2, GPIO_OUT);
	ret |= gpio_set_direction(&dev->gpio_dev, dev->gpio_mode3, GPIO_OUT);
	ret |= gpio_set_direction(&dev->gpio_dev, dev->gpio_dclk0, GPIO_OUT);
	ret |= gpio_set_direction(&dev->gpio_dev, dev->gpio_dclk1, GPIO_OUT);
	ret |= gpio_set_direction(&dev->gpio_dev, dev->gpio_dclk2, GPIO_OUT);
	ret |= gpio_set_direction(&dev->gpio_dev, dev->gpio_sync_in, GPIO_OUT);
	ret |= gpio_set_value(&dev->gpio_dev, dev->gpio_sync_in, GPIO_HIGH);
	ret |= gpio_set_direction(&dev->gpio_dev, dev->gpio_convst_sar, GPIO_OUT);
	ret |= gpio_set_value(&dev->gpio_dev, dev->gpio_convst_sar, GPIO_HIGH);
*/
	// Device Settings
	dev->ctrl_mode = init_param.ctrl_mode;
	dev->spi_crc_en = AD7779_DISABLE;
	dev->spi_op_mode = AD7779_INT_REG;
	dev->sar_state = AD7779_DISABLE;
	dev->sar_mux = AD7779_AUXAINP_AUXAINN;

  uint8_t reg_data;
  for(uint8_t reg_addr = 0; reg_addr < AD7779_REG_SRC_UPDATE + 1; reg_addr++)
  {
    ret |= ad7779_spi_int_reg_read(dev,reg_addr,&reg_data);
    dev->cached_reg_val[reg_addr] = reg_data;
  }


	if ((dev->ctrl_mode == AD7779_SPI_CTRL) &&
				(init_param.spi_crc_en == AD7779_ENABLE)) {
		ret |= ad7779_spi_int_reg_read(dev,
							AD7779_REG_GEN_ERR_REG_1_EN,
							&dev->cached_reg_val[AD7779_REG_GEN_ERR_REG_1_EN]);
		ret |= ad7779_spi_int_reg_write_mask(dev,
							AD7779_REG_GEN_ERR_REG_1_EN,
							AD7779_SPI_CRC_TEST_EN,
							AD7779_SPI_CRC_TEST_EN);
		dev->spi_crc_en = AD7779_ENABLE;
	}


	if (dev->ctrl_mode == AD7779_SPI_CTRL)
		for (i = AD7779_REG_CH_CONFIG(0); i <= AD7779_REG_SRC_UPDATE; i++)
			ret |= ad7779_spi_int_reg_read(dev, i, &dev->cached_reg_val[i]);

  if(0)
	for (i = AD7779_CH0; i <= AD7779_CH7; i++) {
		dev->state[i] = init_param.state[i];
		if (dev->ctrl_mode == AD7779_SPI_CTRL)
			ret |= ad7779_set_state(dev, (ad7779_ch)i, dev->state[i]);
	}
 
	for (i = AD7779_CH0; i <= AD7779_CH7; i++) {
		dev->gain[i] = init_param.gain[i];
		if (dev->ctrl_mode == AD7779_SPI_CTRL)
			ret |= ad7779_set_gain(dev, (ad7779_ch)i, dev->gain[i]);
	}

	dev->dec_rate_int = init_param.dec_rate_int;
	dev->dec_rate_dec = init_param.dec_rate_dec;
	if (dev->ctrl_mode == AD7779_SPI_CTRL)
		ret |= ad7779_set_dec_rate(dev, dev->dec_rate_int, dev->dec_rate_dec);

 	dev->ref_type = init_param.ref_type;
	if (dev->ctrl_mode == AD7779_SPI_CTRL)
		ret |= ad7779_set_reference_type(dev, dev->ref_type);

	dev->pwr_mode = init_param.pwr_mode;
	if (dev->ctrl_mode == AD7779_SPI_CTRL)
		ret |= ad7779_set_power_mode(dev, dev->pwr_mode);

	if (dev->ctrl_mode == AD7779_PIN_CTRL) {
		ret |= ad7779_do_update_mode_pins(dev);
	}

  /*
	dev->dclk_div = init_param.dclk_div;
	ad7779_set_dclk_div(dev, dev->dclk_div);

	for (i = AD7779_CH0; i <= AD7779_CH7; i++) {
		dev->sync_offset[i] = init_param.sync_offset[i];
		dev->offset_corr[i] = init_param.offset_corr[i];
		dev->gain_corr[i] = init_param.gain_corr[i];
		if (dev->ctrl_mode == AD7779_SPI_CTRL) {
			ret |= ad7779_set_sync_offset(dev, (ad7779_ch)i,
								dev->sync_offset[i]);
			ret |= ad7779_set_offset_corr(dev, (ad7779_ch)i,
								dev->offset_corr[i]);
			ret |= ad7779_set_gain_corr(dev, (ad7779_ch)i,
								dev->gain_corr[i]);
		}
	}
*/
	*device = dev;

	if (!ret)
	{
//	  print_text("AD7779 successfully initialized\n");
//  printf("AD7779 successfully initialized\n");
	}
  else
  {
//    char str_in[] = "AD7779 initialization error (%d)   \n";
//    char str_out[] = "AD7779 initialization error (%d)   \n";
//    sprintf(str_out, str_in, ret);
//    print_text(str_out);
//  printf("AD7779 initialization error (%d)\n", ret);
  }

	return ret;
}
